patdie421/pct-connectors-rebuild/images/2e-mb-1986-2.webp

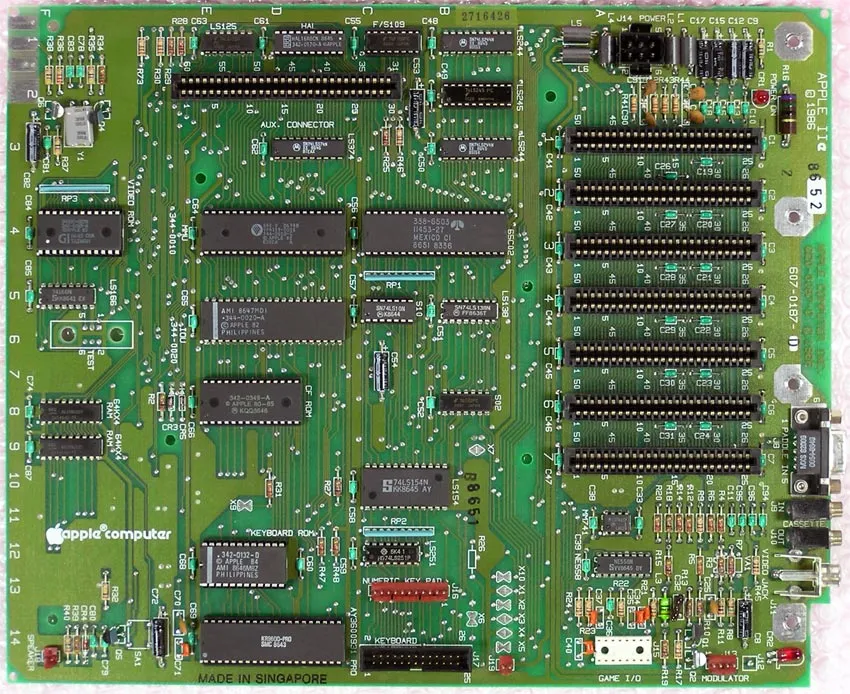
images/2e-mb-1986-2.webp
